danboid/uzebox-omega/cad/Enclosures/fightstick/Uzebox-joystick-buttons.jpg

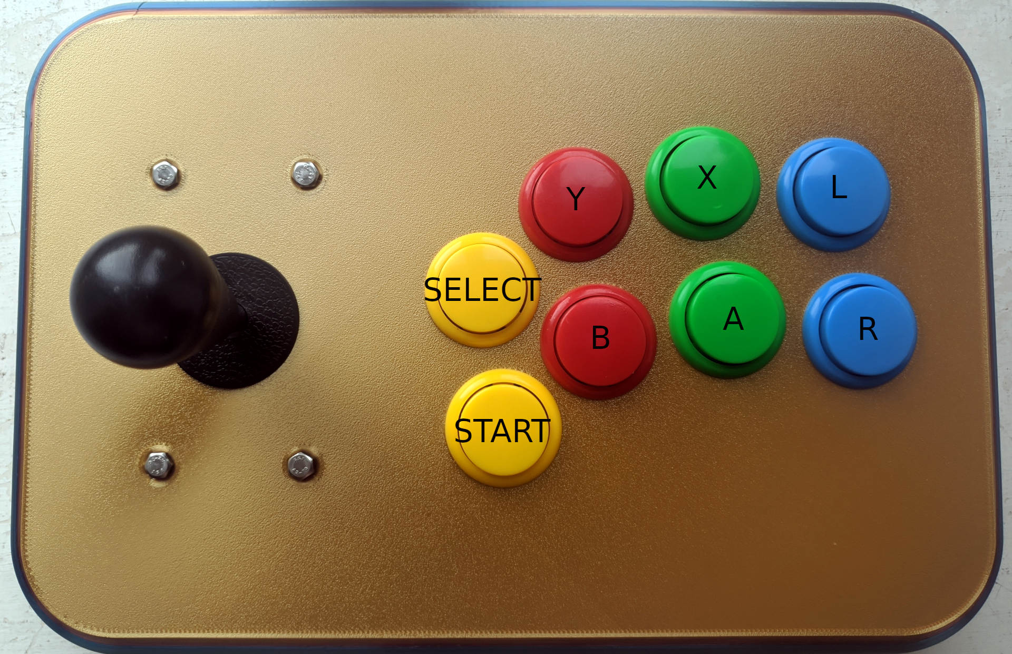
cad/Enclosures/fightstick/Uzebox-joystick-buttons.jpg
