danboid/uzebox-omega/cad/Enclosures/fightstick/Uzebox-joystick-V4.jpg

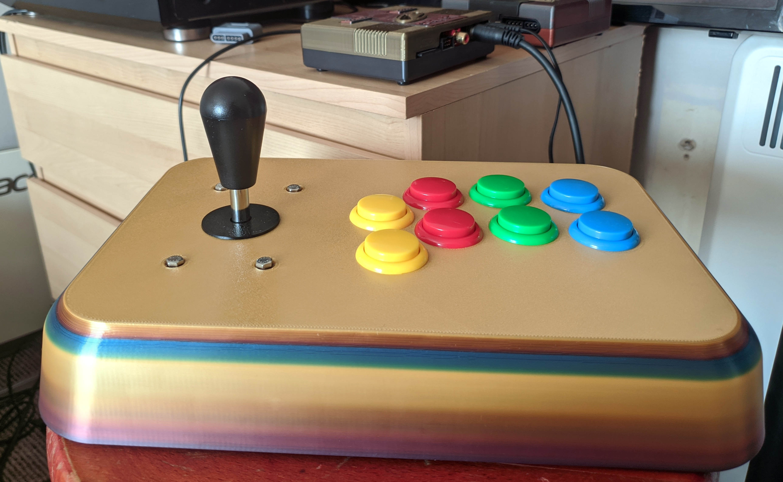
cad/Enclosures/fightstick/Uzebox-joystick-V4.jpg
