danboid/uzebox-omega/schematics/Uzebox-Omega/V1.1.1/assets/Uzebo-V5_0-PCB.png

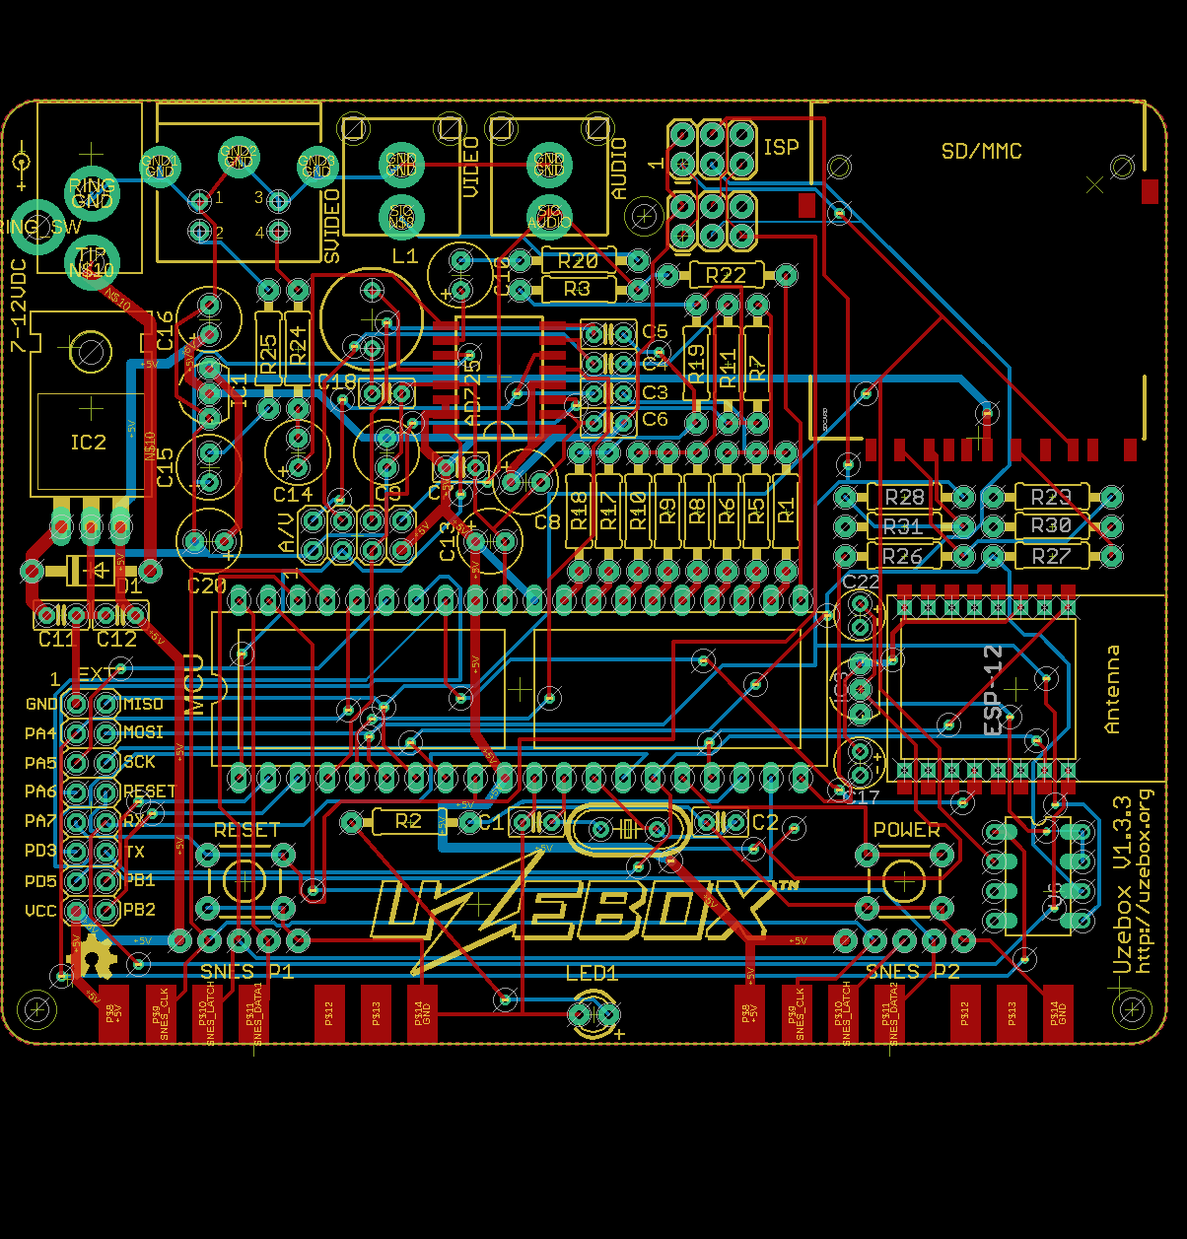
schematics/Uzebox-Omega/V1.1.1/assets/Uzebo-V5_0-PCB.png
