danboid/uzebox-omega/schematics/Uzebox-Omega/V1.1.1/assets/uzebox-1.jpg

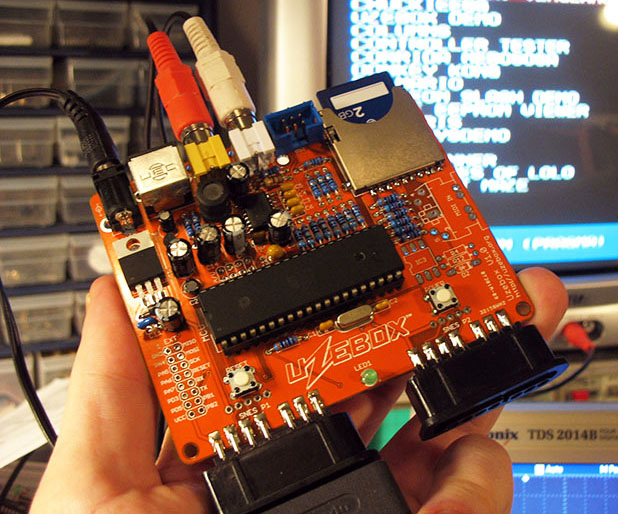
schematics/Uzebox-Omega/V1.1.1/assets/uzebox-1.jpg
