danboid/uzebox-omega/schematics/Uzebox-Omega/V1.1.1/assets/uzebox-pcb-2.png

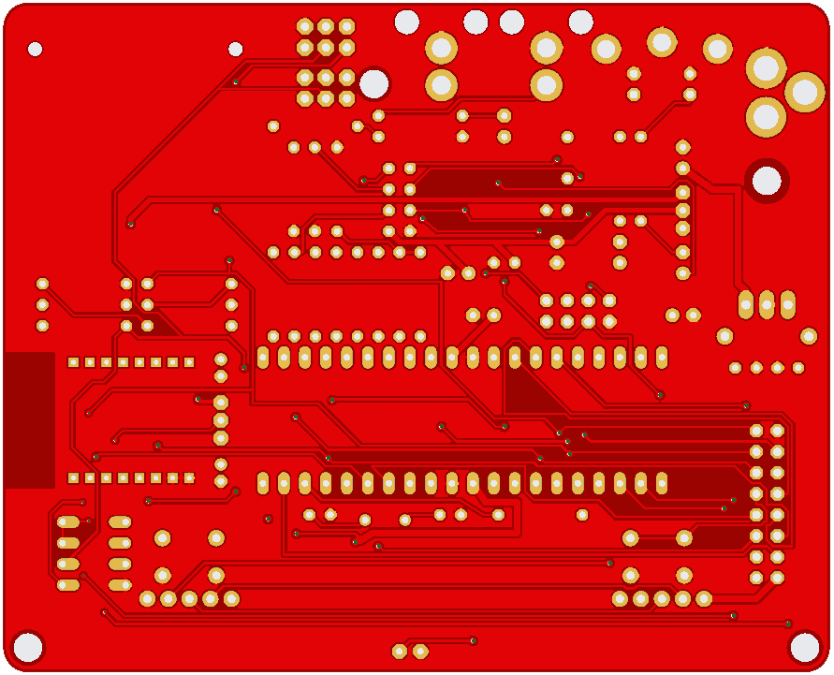
schematics/Uzebox-Omega/V1.1.1/assets/uzebox-pcb-2.png
