danboid/uzebox-omega/Uzebox-Omega-v1.1.1-PCB-photo.jpg

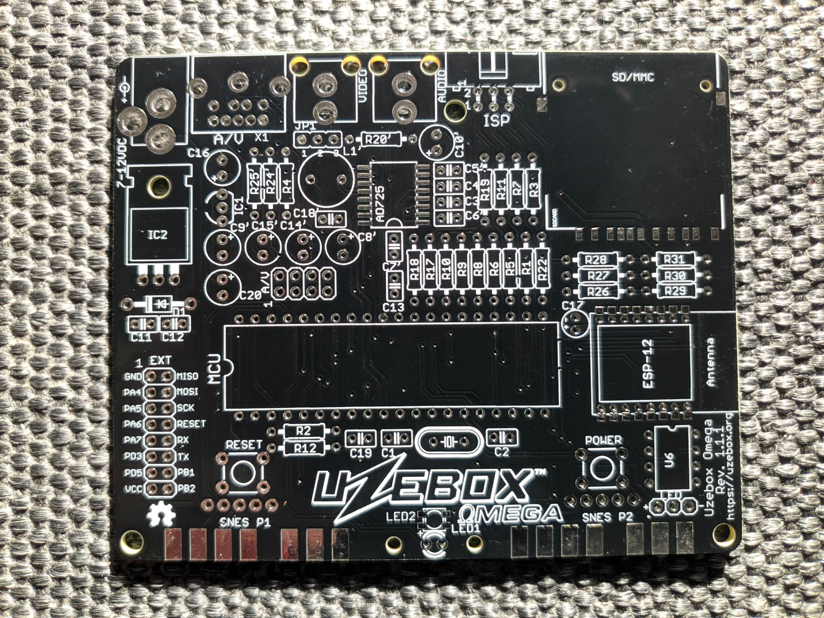
Uzebox-Omega-v1.1.1-PCB-photo.jpg
