danboid/uzebox-omega/cad/Enclosures/fightstick/Uzebox-joystick-sanwa-wiring-labels.jpg

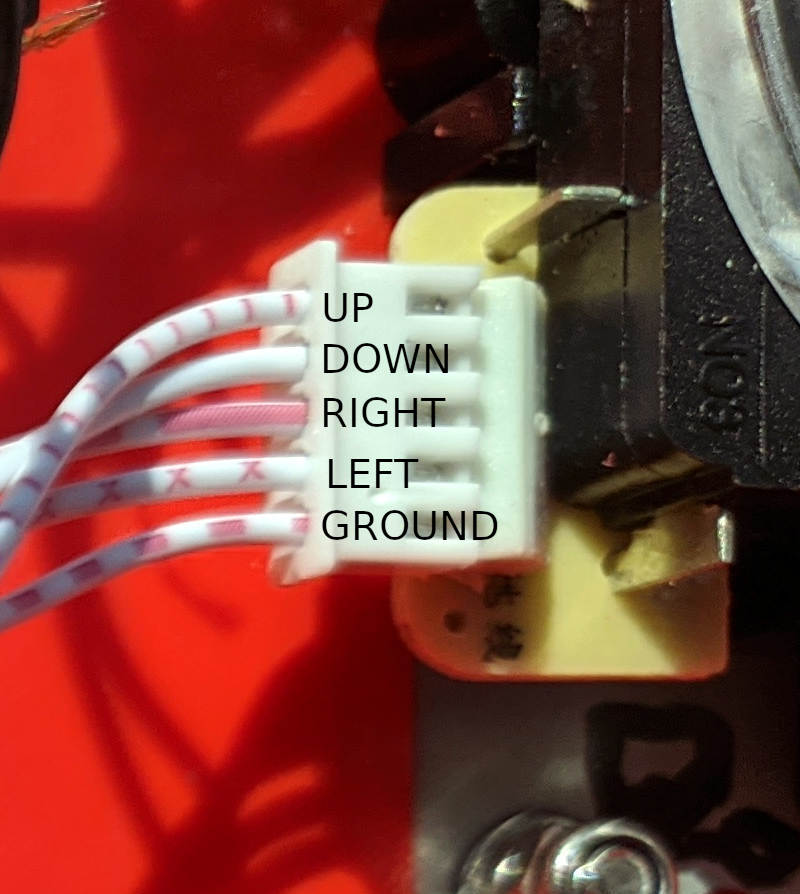
cad/Enclosures/fightstick/Uzebox-joystick-sanwa-wiring-labels.jpg
