danboid/uzebox-omega/cad/Enclosures/fightstick/Uzebox-joystick-sanwa-wiring.jpg

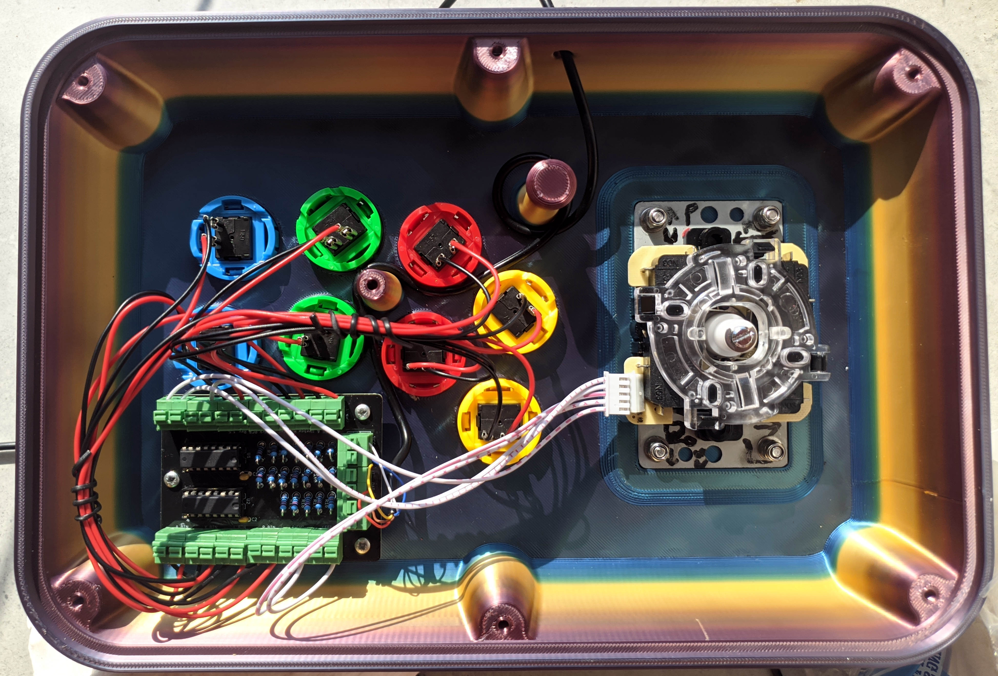
cad/Enclosures/fightstick/Uzebox-joystick-sanwa-wiring.jpg
