danboid/uzebox-omega/schematics/Uzebox-Omega/V1.1.1/assets/guide/image6.jpg

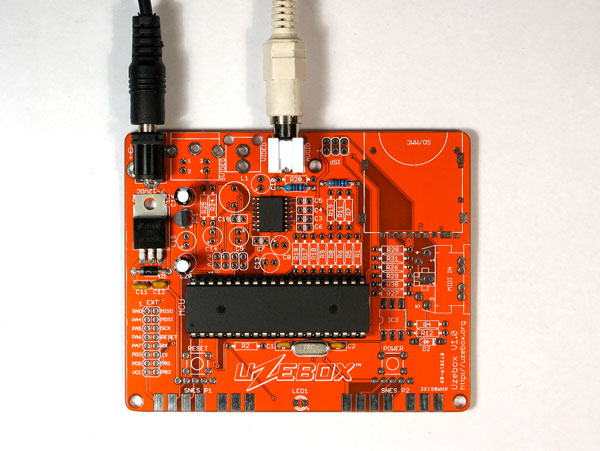
schematics/Uzebox-Omega/V1.1.1/assets/guide/image6.jpg
