danboid/uzebox-omega/schematics/Uzebox-Omega/V1.1.1/assets/guide/image25.png

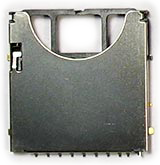
schematics/Uzebox-Omega/V1.1.1/assets/guide/image25.png
