danboid/uzebox-omega/schematics/Uzebox-Omega/V1.1.1/assets/guide/image56.jpg

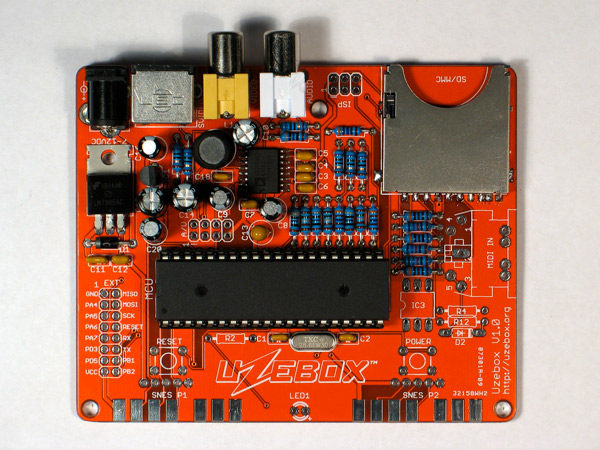
schematics/Uzebox-Omega/V1.1.1/assets/guide/image56.jpg
