danboid/uzebox-omega/schematics/Uzebox-Omega/V1.1.1/assets/guide/image79.png

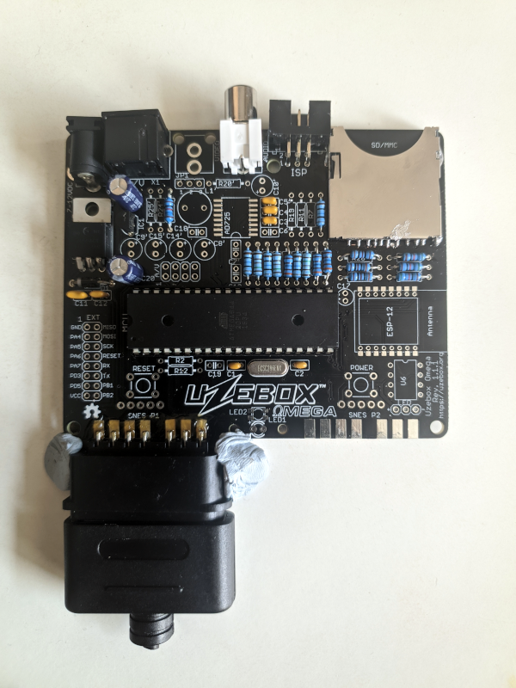
schematics/Uzebox-Omega/V1.1.1/assets/guide/image79.png
